LafeLabs/quantumnoisedotorg/geometron/symbolfeed/symbol1696459947.png

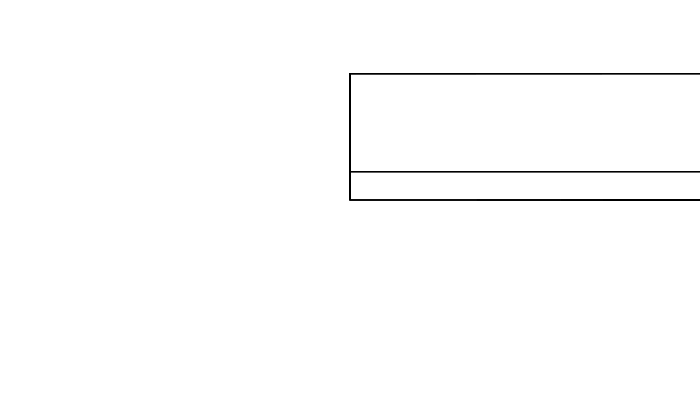
geometron/symbolfeed/symbol1696459947.png
