LafeLabs/quantumnoisedotorg/geometron/symbolfeed/symbol1696465862.png

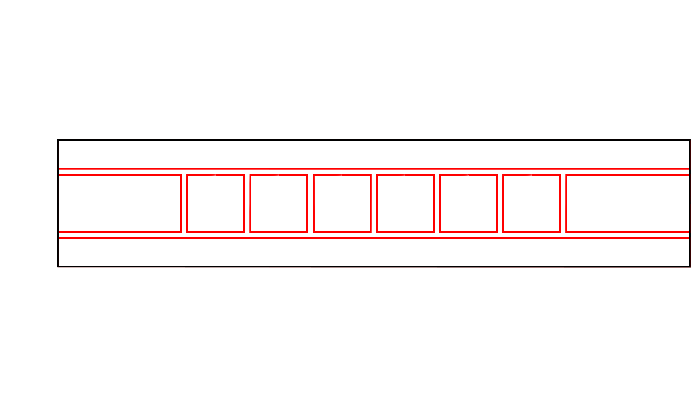
geometron/symbolfeed/symbol1696465862.png
