LafeLabs/quantumnoisedotorg/geometron/symbolfeed/symbol1696466057.png

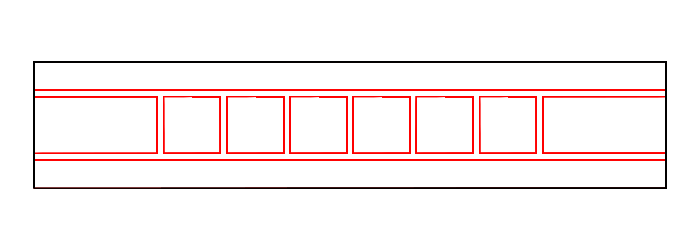
geometron/symbolfeed/symbol1696466057.png
