LafeLabs/quantumnoisedotorg/geometron/symbolfeed/symbol1696466279.png

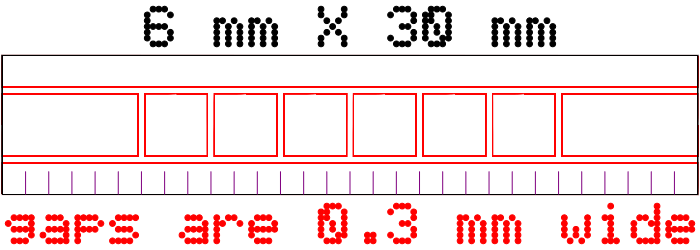
geometron/symbolfeed/symbol1696466279.png
