LafeLabs/quantumnoisedotorg/the-book-of-noise/trashmagic/BOOK-OF-NOISE.png

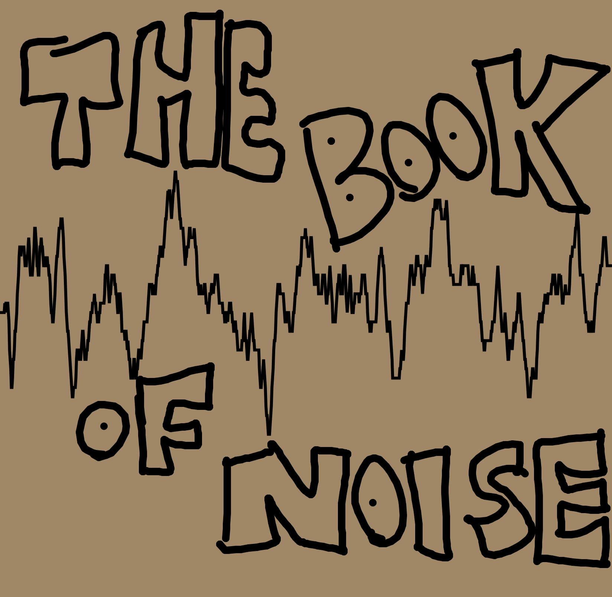
the-book-of-noise/trashmagic/BOOK-OF-NOISE.png
