LafeLabs/quantumnoisedotorg/trashmagic/filter-photo.png

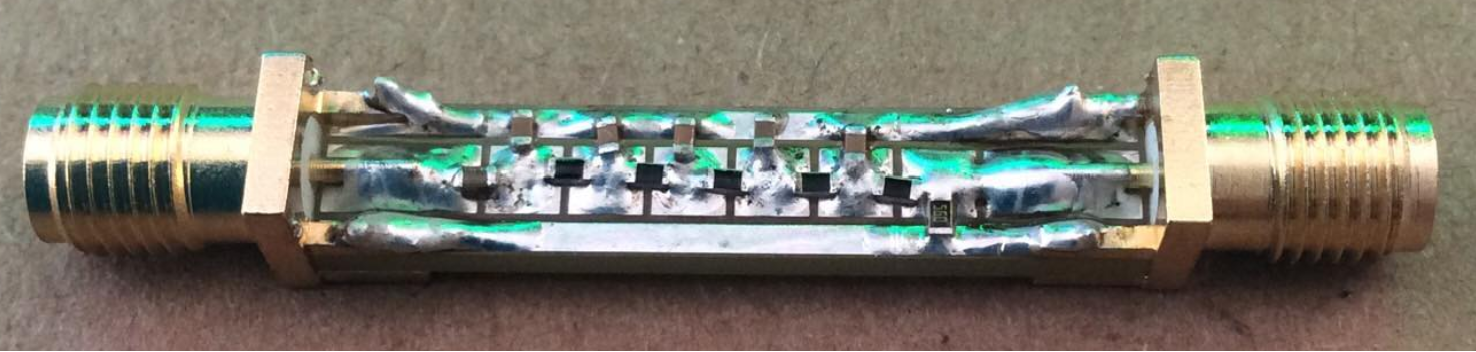
trashmagic/filter-photo.png
