LafeLabs/quantumnoisedotorg/trashmagic/graphene-black-2.png

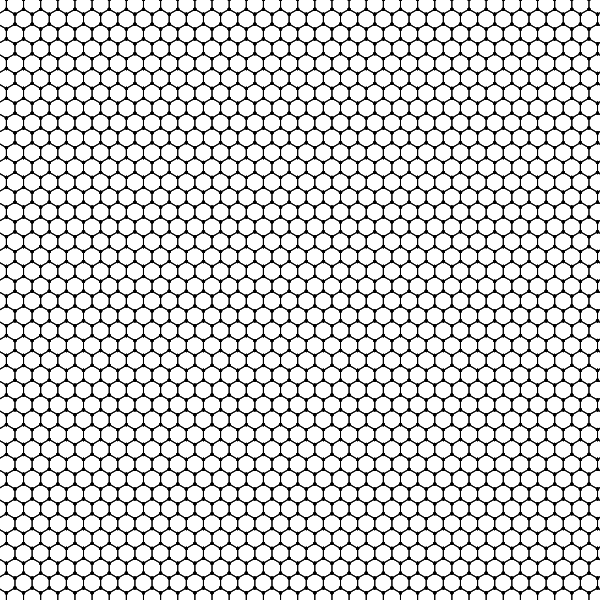
trashmagic/graphene-black-2.png
