LafeLabs/quantumnoisedotorg/trashmagic/graphene-black-3.png

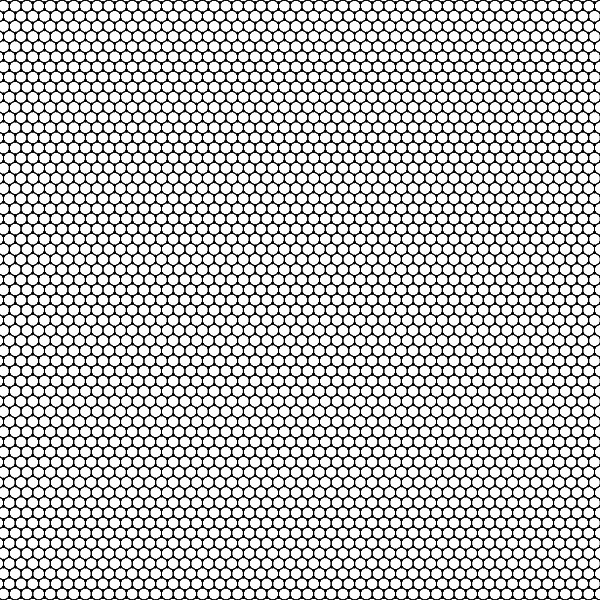
trashmagic/graphene-black-3.png
