LafeLabs/quantumnoisedotorg/trashmagic/graphene-black-4.png

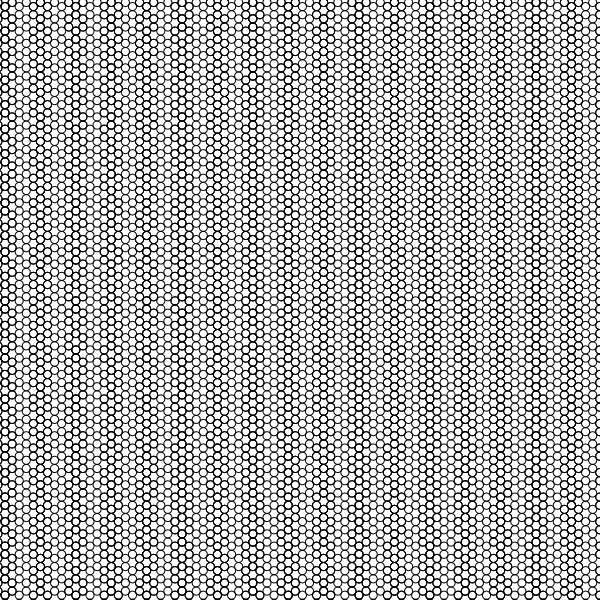
trashmagic/graphene-black-4.png
