LafeLabs/quantumnoisedotorg/trashmagic/graphene-rainbow-1.png

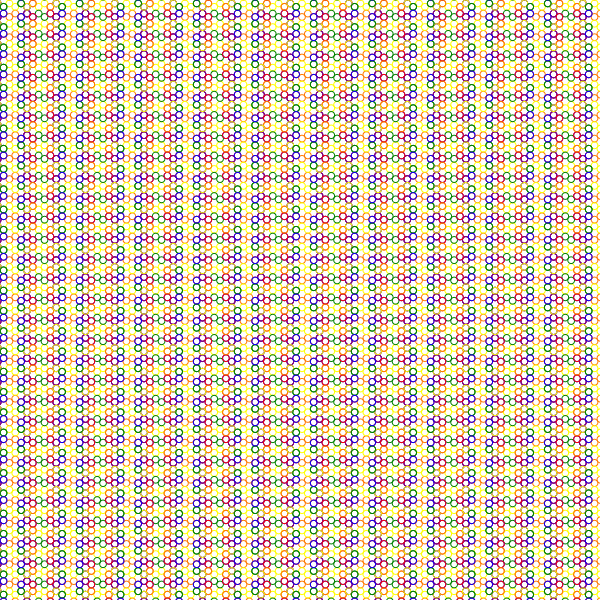
trashmagic/graphene-rainbow-1.png
