LafeLabs/quantumnoisedotorg/trashmagic/merlock/MER_Tarot1.jpg

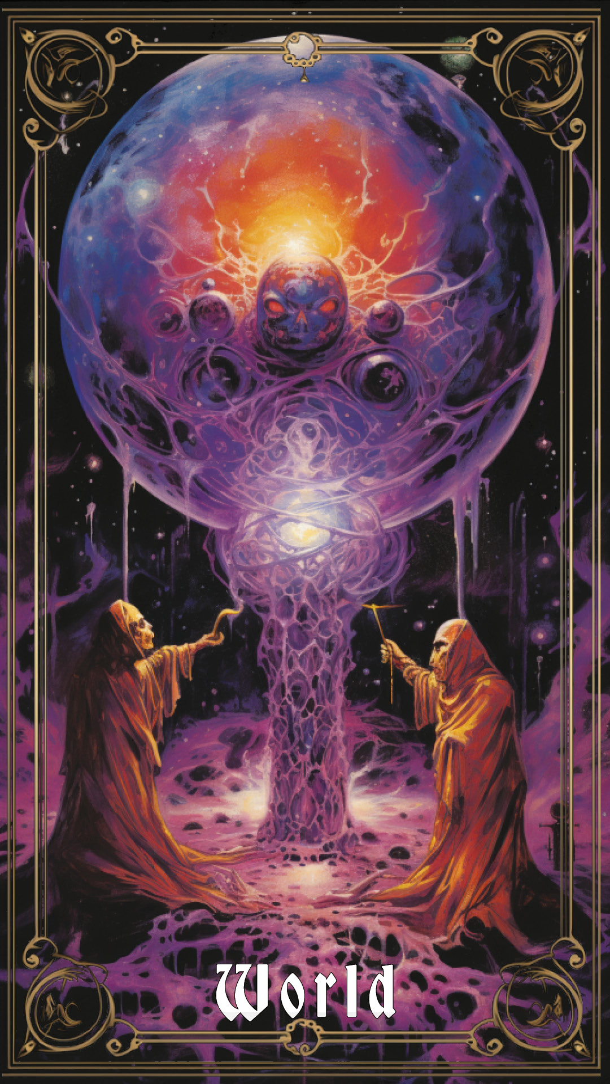
trashmagic/merlock/MER_Tarot1.jpg
