LafeLabs/quantumnoisedotorg/trashmagic/merlock/MER_Tarot3.jpg

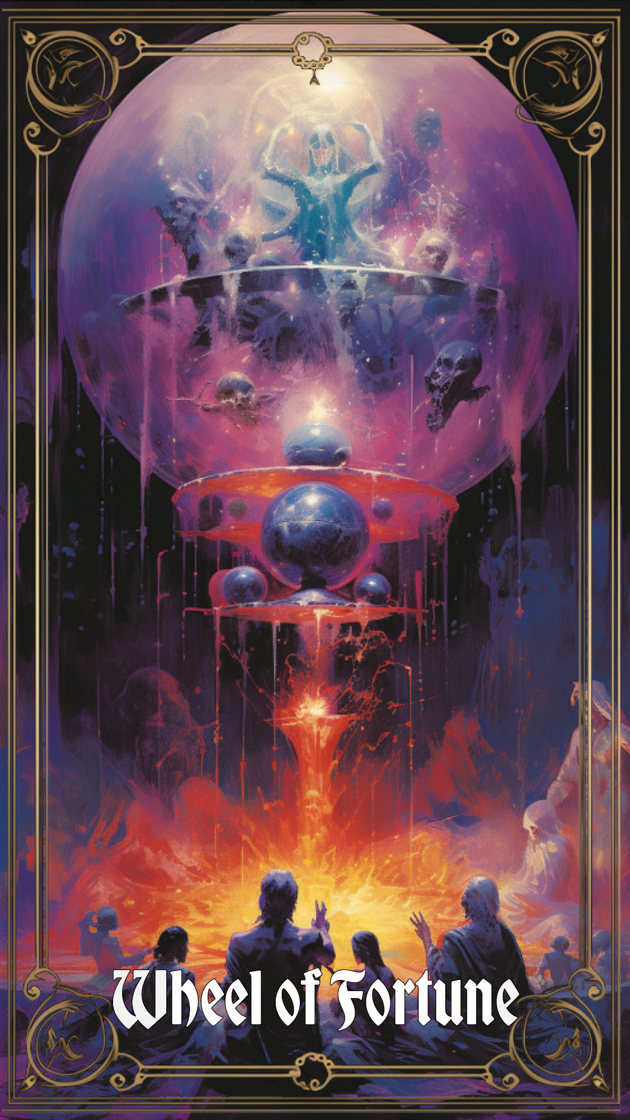
trashmagic/merlock/MER_Tarot3.jpg
