LafeLabs/quantumnoisedotorg/trashmagic/merlock/MER_Tarot4.jpg

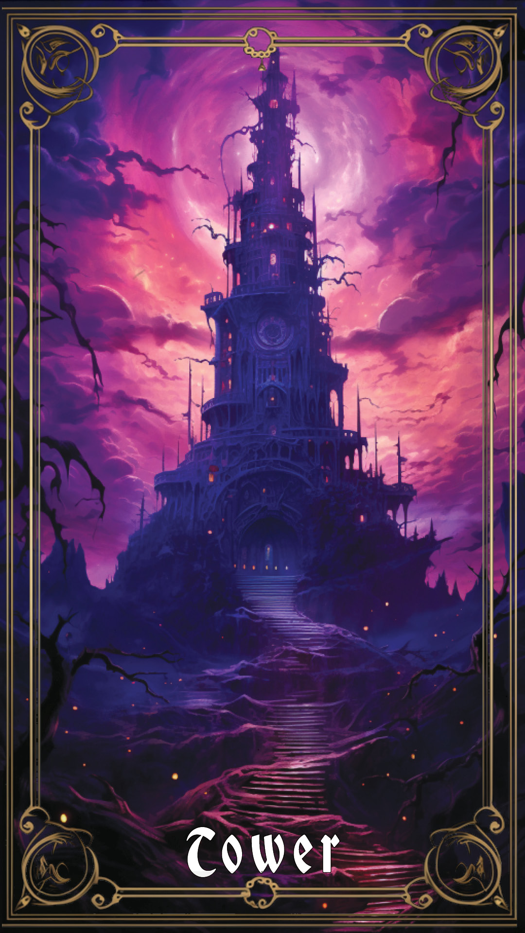
trashmagic/merlock/MER_Tarot4.jpg
