LafeLabs/quantumnoisedotorg/trashmagic/merlock/MER_Tarot5.jpg

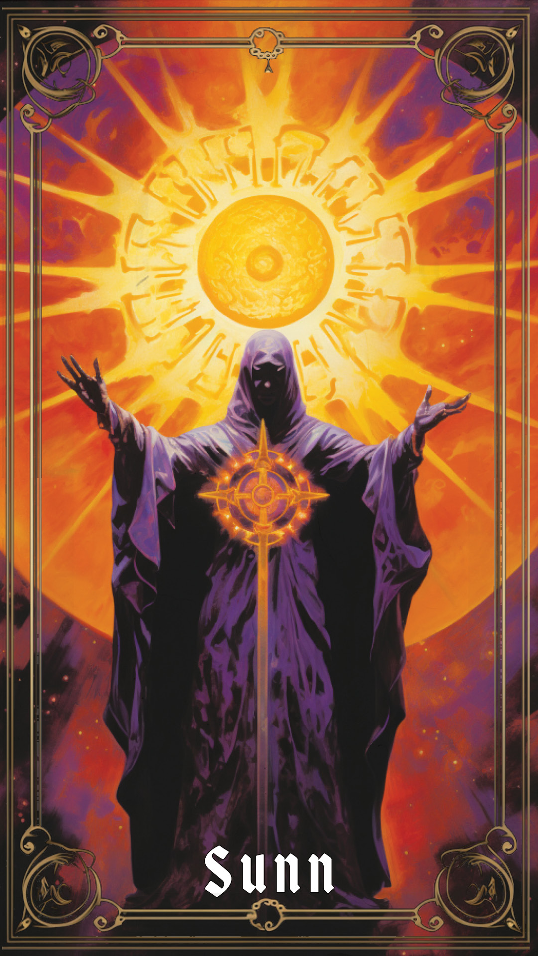
trashmagic/merlock/MER_Tarot5.jpg
