LafeLabs/quantumnoisedotorg/trashmagic/merlock/MER_Tarot6.jpg

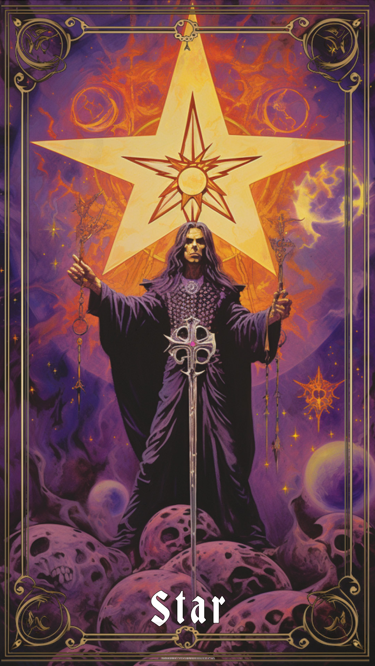
trashmagic/merlock/MER_Tarot6.jpg
