LafeLabs/quantumnoisedotorg/trashmagic/merlock/MER_Tarot7.jpg

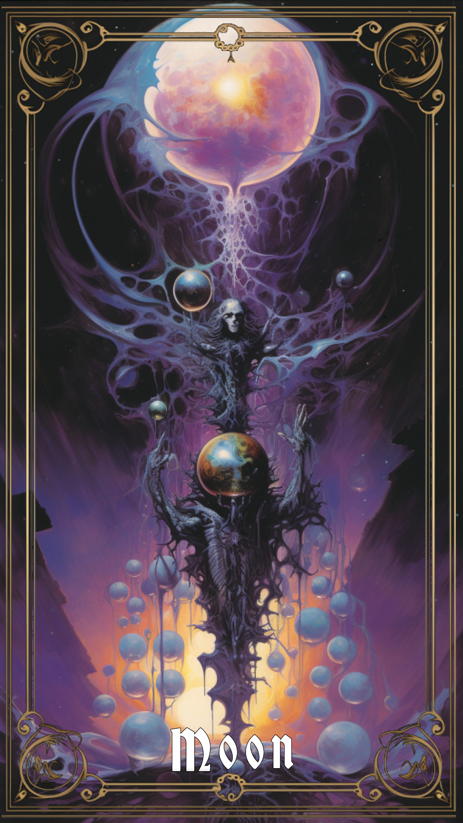
trashmagic/merlock/MER_Tarot7.jpg
