LafeLabs/quantumnoisedotorg/trashmagic/merlock/MER_Tarot8.jpg

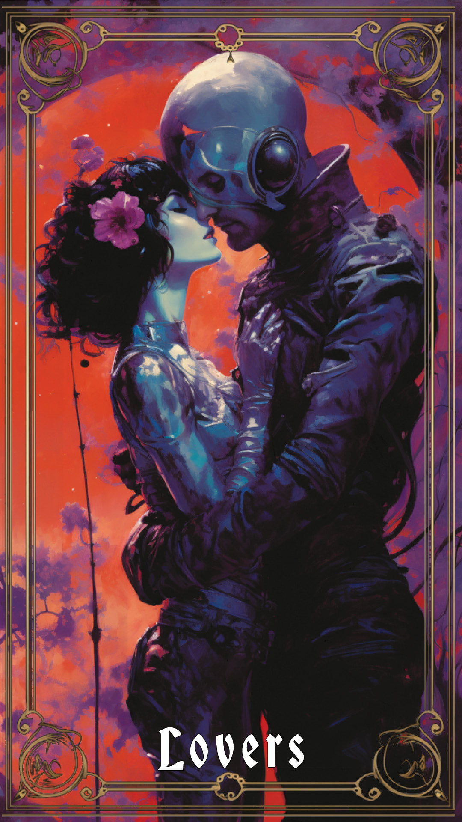
trashmagic/merlock/MER_Tarot8.jpg
