LafeLabs/quantumnoisedotorg/trashmagic/merlock/MER_Tarot9.jpg

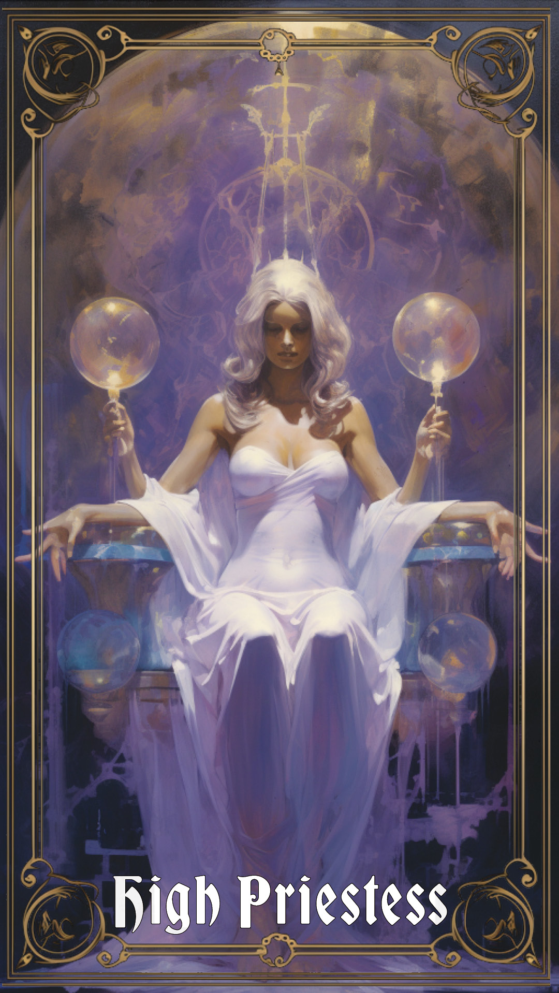
trashmagic/merlock/MER_Tarot9.jpg
