LafeLabs/quantumnoisedotorg/trashmagic/merlock/MER_Tarot10.jpg

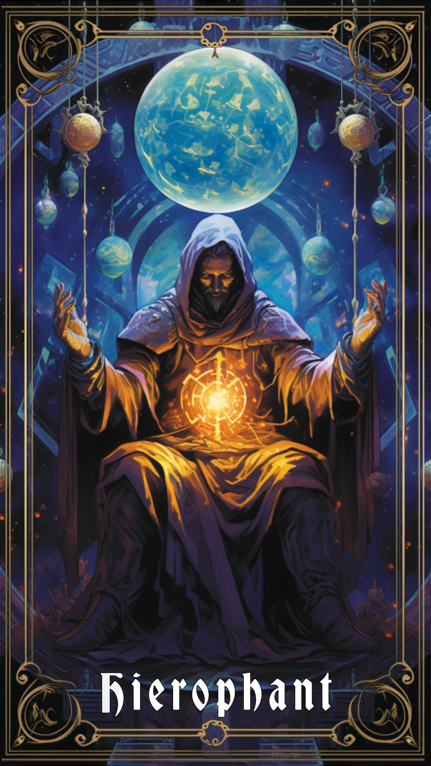
trashmagic/merlock/MER_Tarot10.jpg
