LafeLabs/quantumnoisedotorg/trashmagic/merlock/MER_Tarot11.jpg

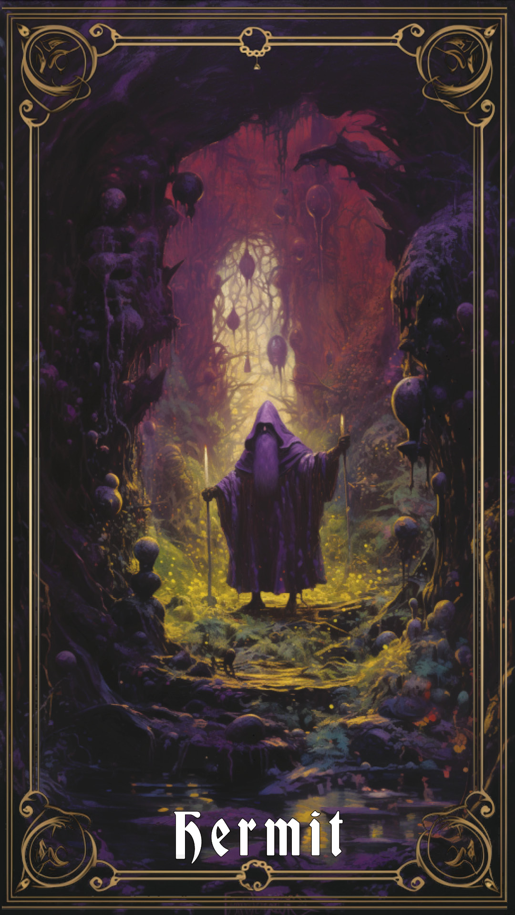
trashmagic/merlock/MER_Tarot11.jpg
