LafeLabs/quantumnoisedotorg/trashmagic/merlock/MER_Tarot12.jpg

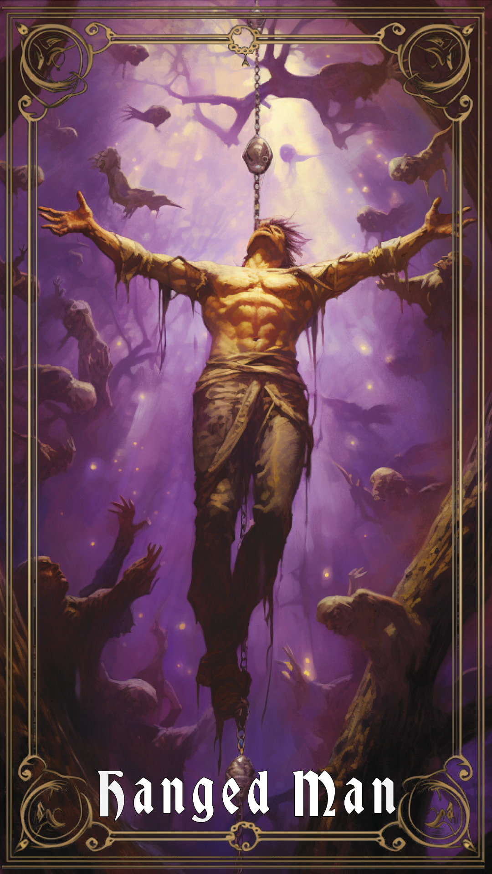
trashmagic/merlock/MER_Tarot12.jpg
