LafeLabs/quantumnoisedotorg/trashmagic/merlock/MER_Tarot14.jpg

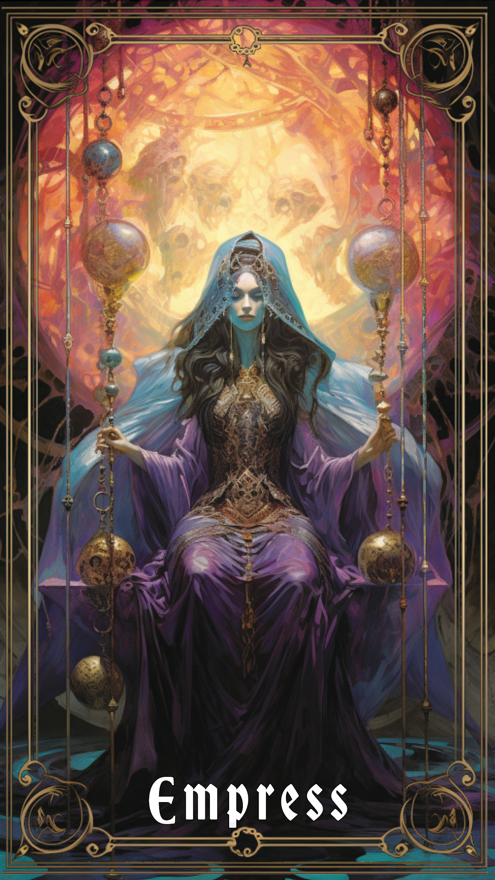
trashmagic/merlock/MER_Tarot14.jpg
