LafeLabs/quantumnoisedotorg/trashmagic/merlock/MER_Tarot15.jpg

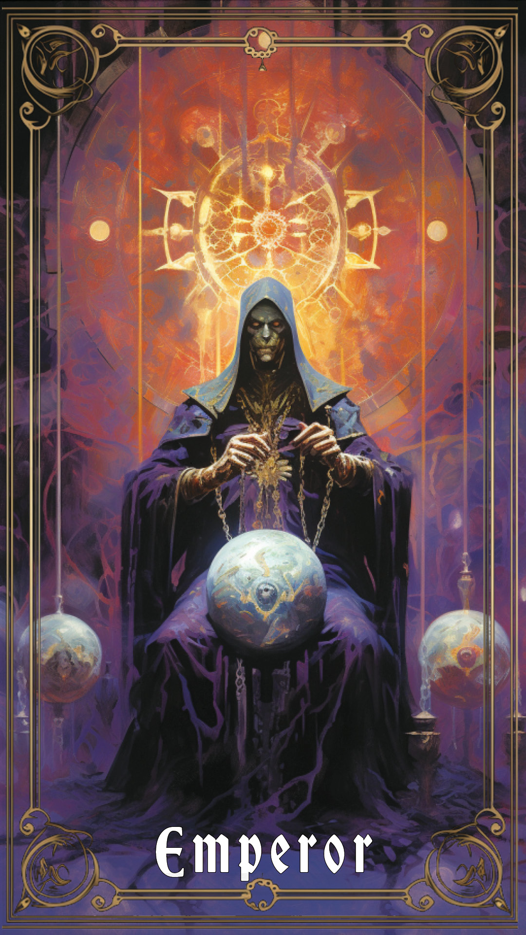
trashmagic/merlock/MER_Tarot15.jpg
