LafeLabs/quantumnoisedotorg/trashmagic/merlock/MER_Tarot16.jpg

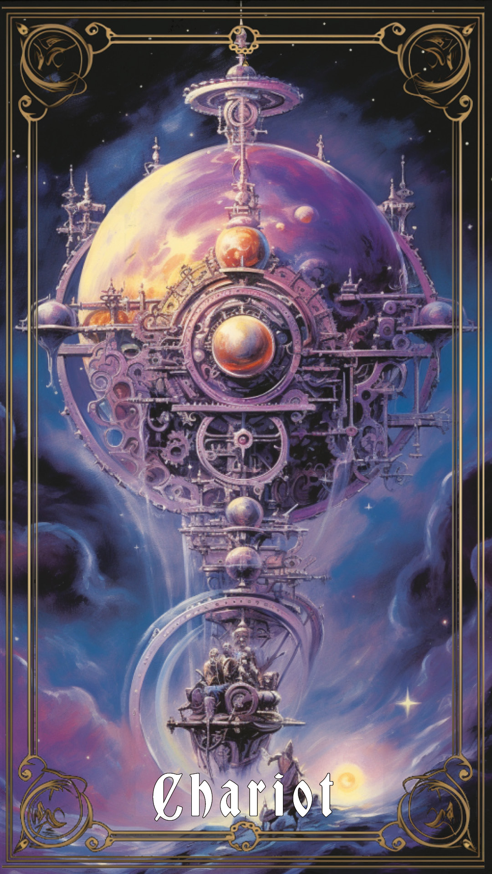
trashmagic/merlock/MER_Tarot16.jpg
