LafeLabs/quantumnoisedotorg/trashmagic/merlock/MER_Tarot17.jpg

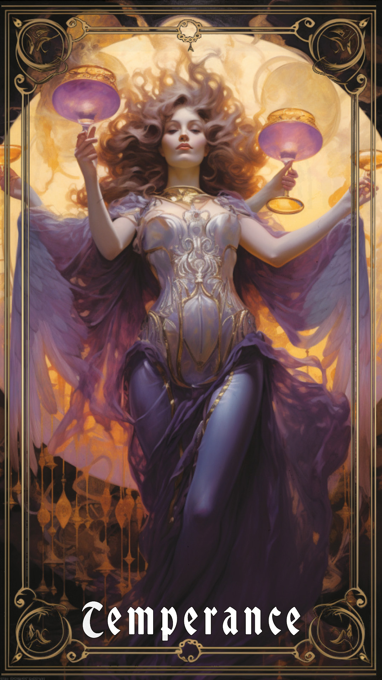
trashmagic/merlock/MER_Tarot17.jpg
