LafeLabs/quantumnoisedotorg/trashmagic/merlock/MER_Tarot18.jpg

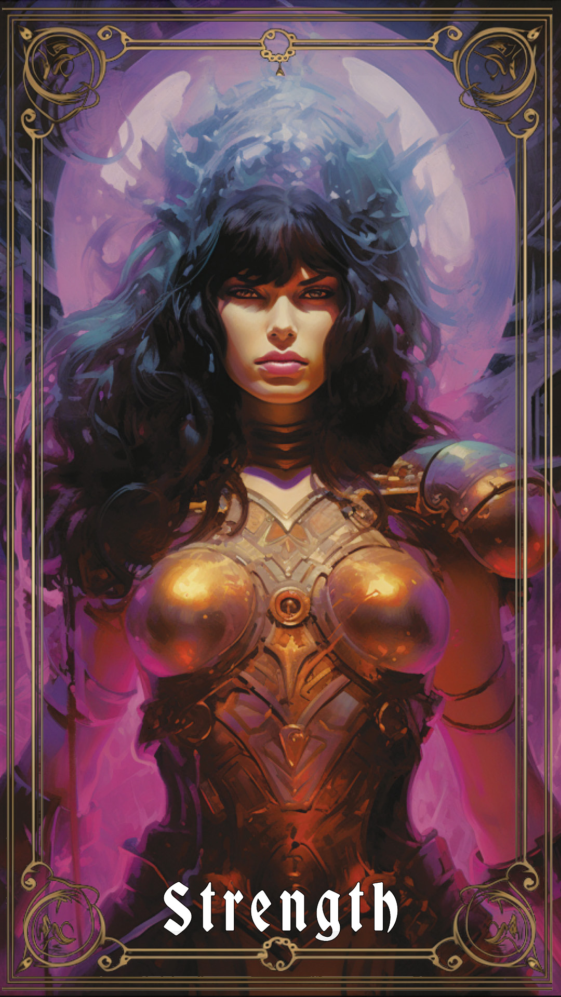
trashmagic/merlock/MER_Tarot18.jpg
