LafeLabs/quantumnoisedotorg/trashmagic/merlock/MER_Tarot19.jpg

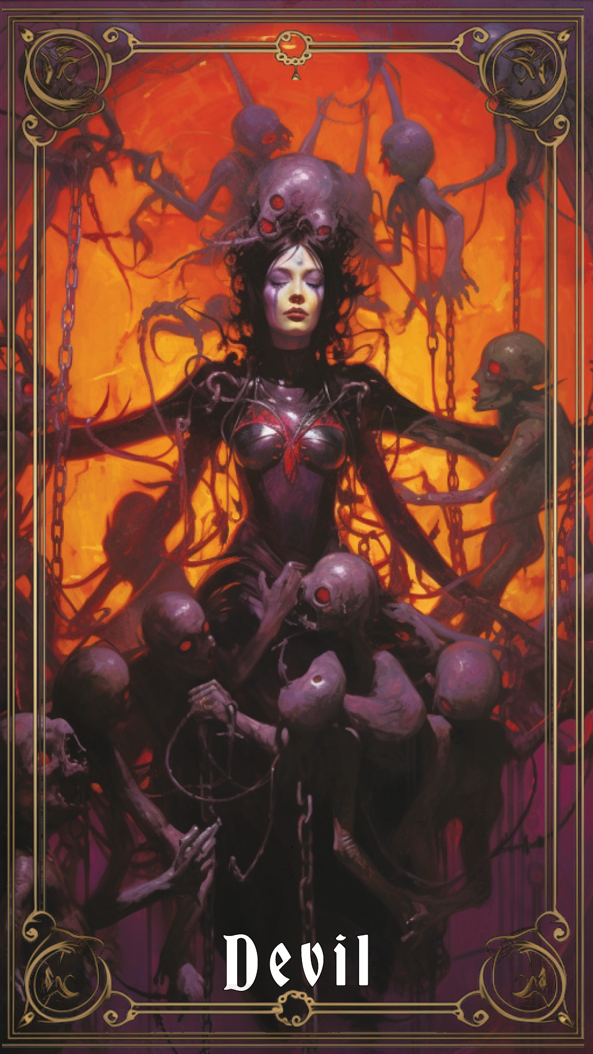
trashmagic/merlock/MER_Tarot19.jpg
