LafeLabs/quantumnoisedotorg/trashmagic/merlock/MER_Tarot20.jpg

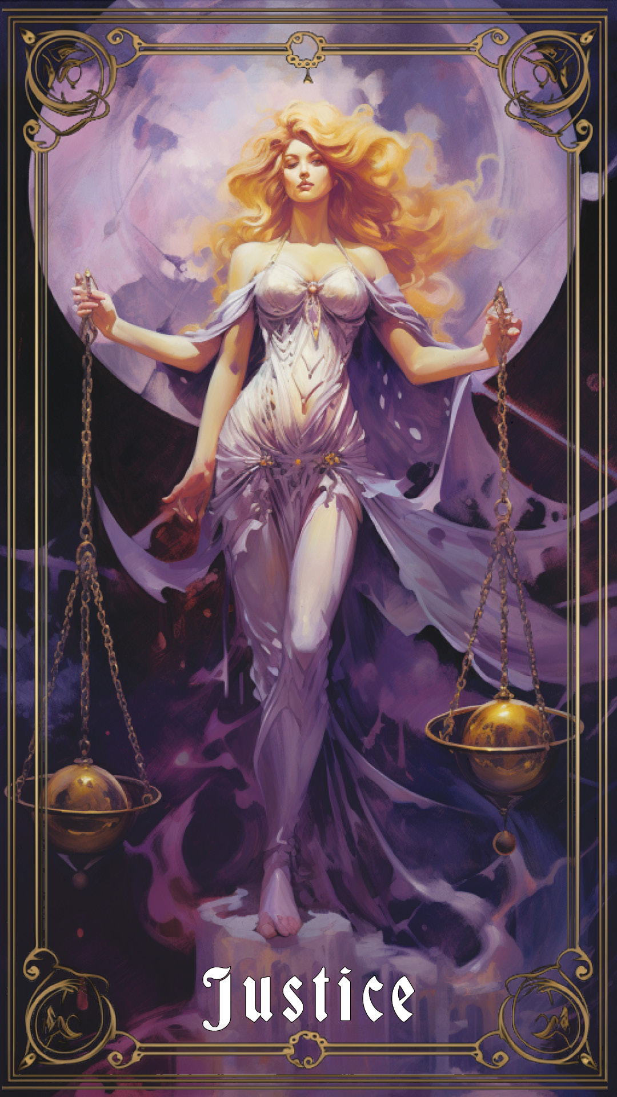
trashmagic/merlock/MER_Tarot20.jpg
