LafeLabs/quantumnoisedotorg/trashmagic/merlock/MER_Tarot22.jpg

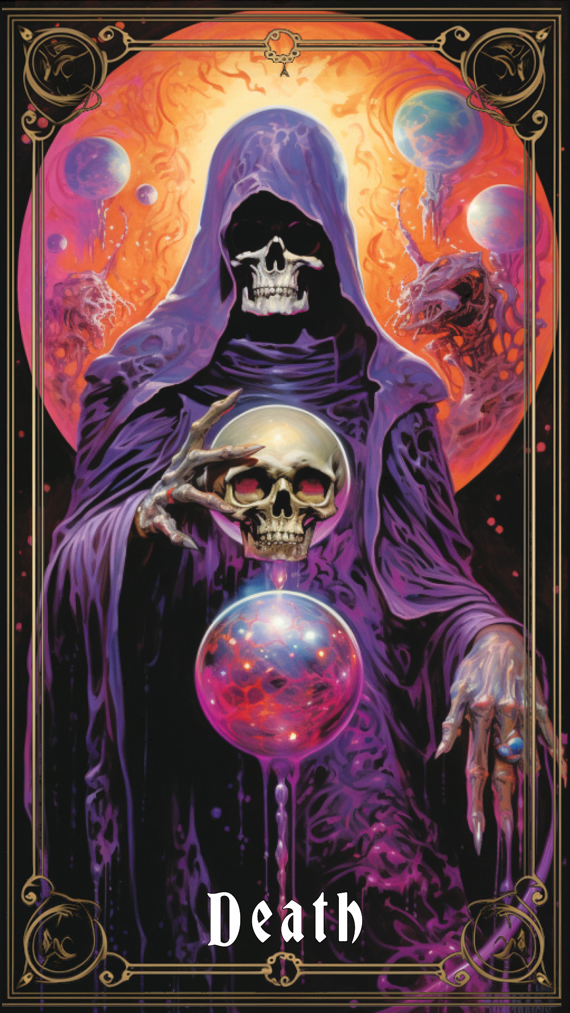
trashmagic/merlock/MER_Tarot22.jpg
