LafeLabs/quantumnoisedotorg/trashmagic/pcb-launch-photo2.png

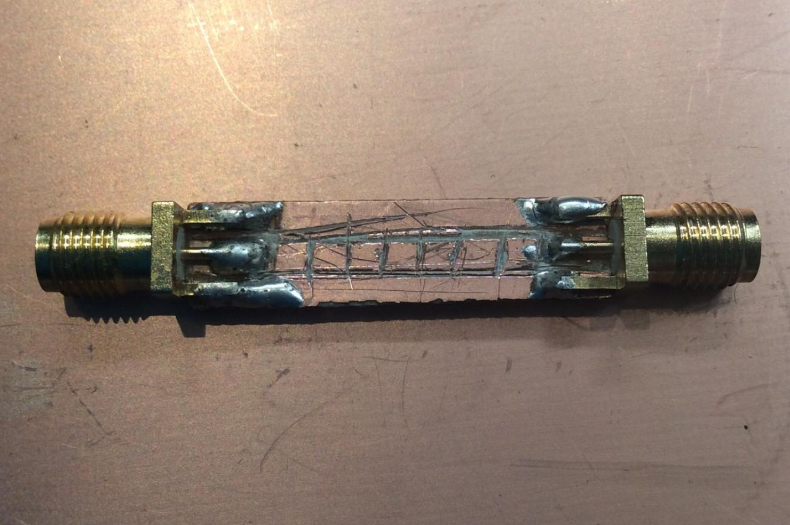
trashmagic/pcb-launch-photo2.png
