LafeLabs/quantumnoisedotorg/trashmagic/pcb-layout-screenshot.png

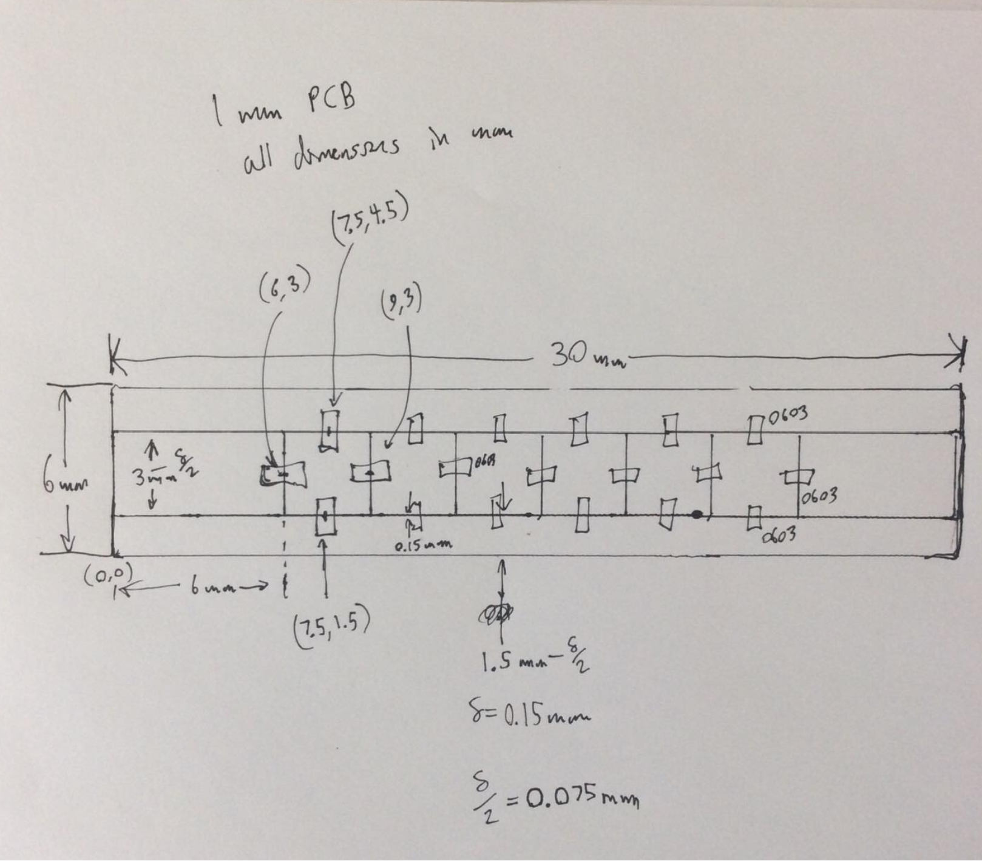
trashmagic/pcb-layout-screenshot.png
