LafeLabs/quantumnoisedotorg/trashmagic/QCHAIN1.png

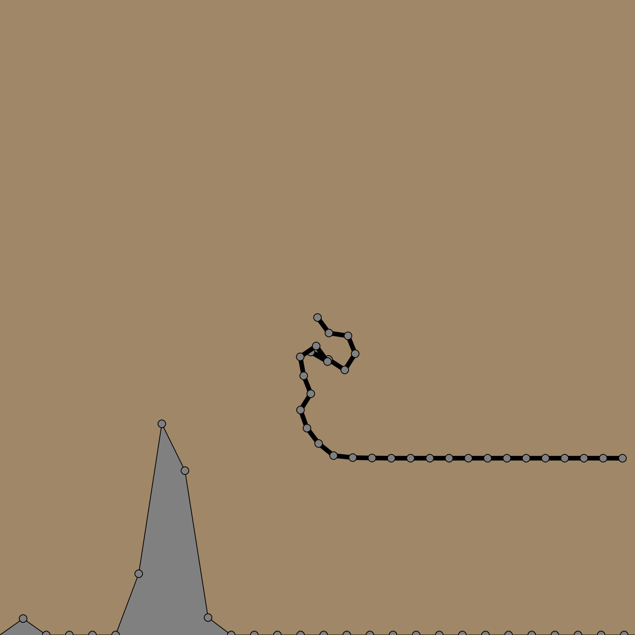
trashmagic/QCHAIN1.png
