LafeLabs/quantumnoisedotorg/trashmagic/QCHAIN2.png

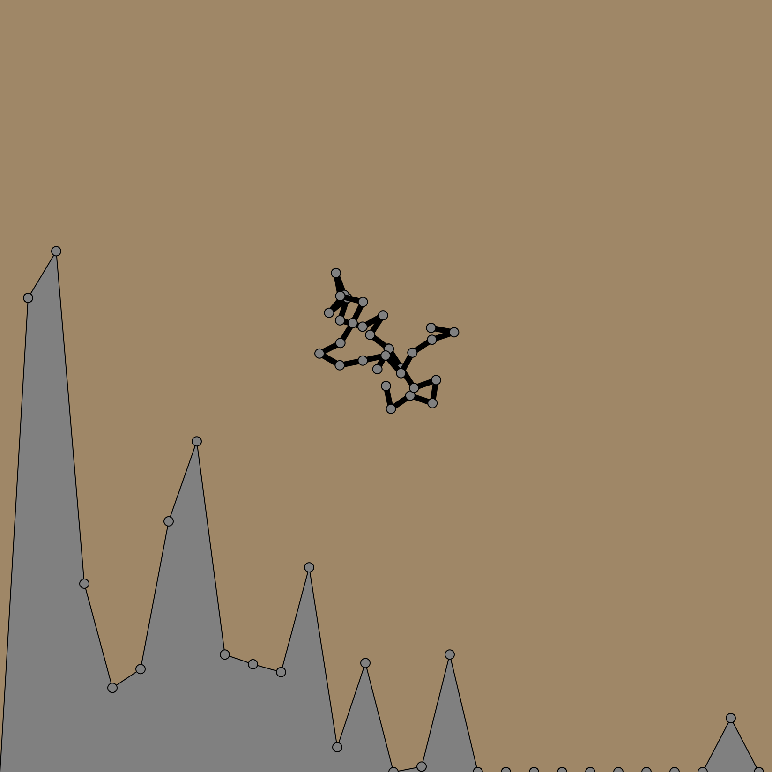
trashmagic/QCHAIN2.png
