LafeLabs/quantumnoisedotorg/trashmagic/QCHAIN3.png

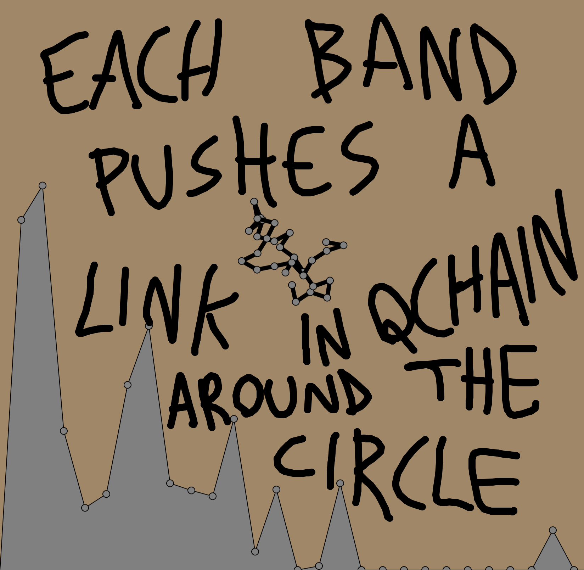
trashmagic/QCHAIN3.png
