LafeLabs/quantumnoisedotorg/trashmagic/rampsquare1.png

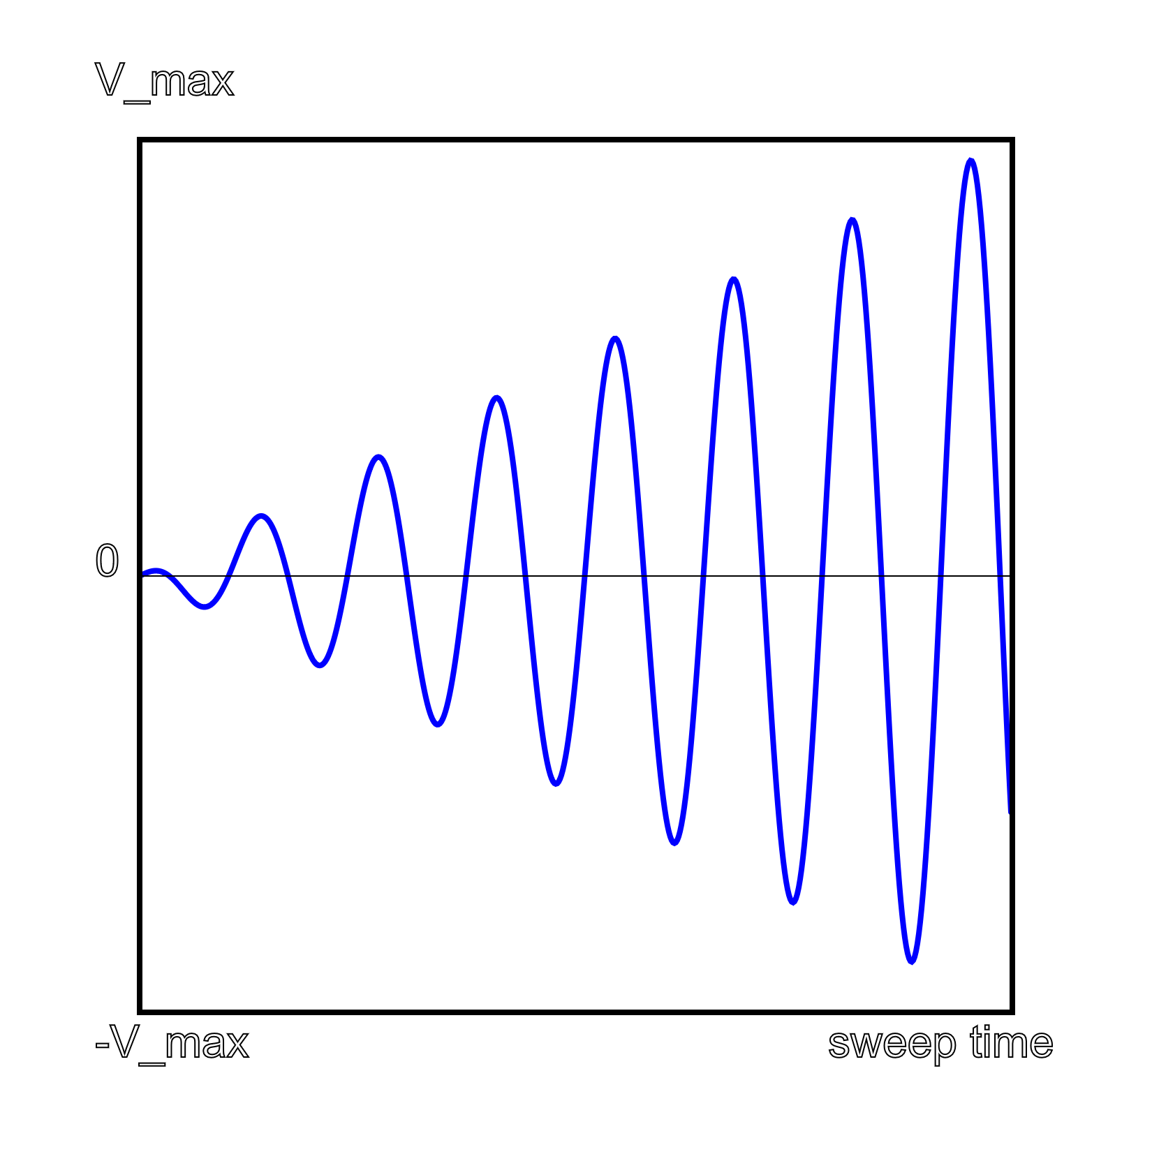
trashmagic/rampsquare1.png
