LafeLabs/quantumnoisedotorg/trashmagic/rampsquare2.png

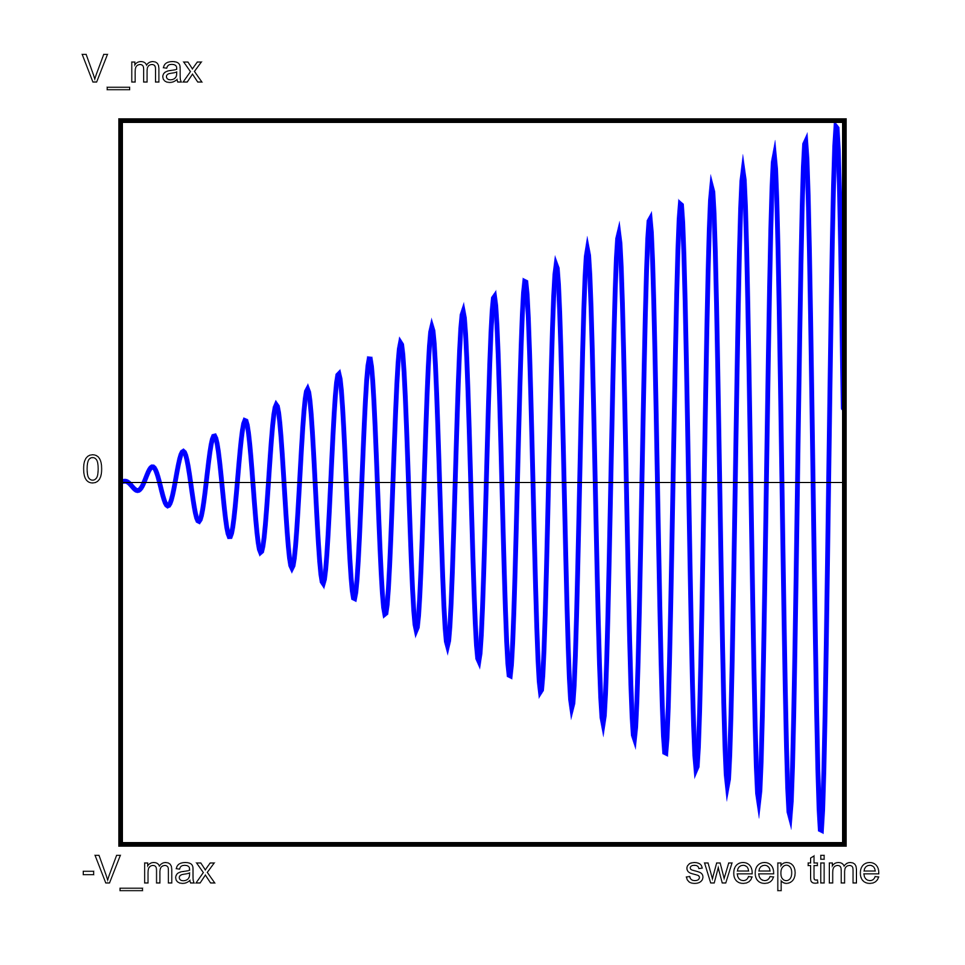
trashmagic/rampsquare2.png
