LafeLabs/quantumnoisedotorg/trashmagic/rock-n-roll-plots2.png

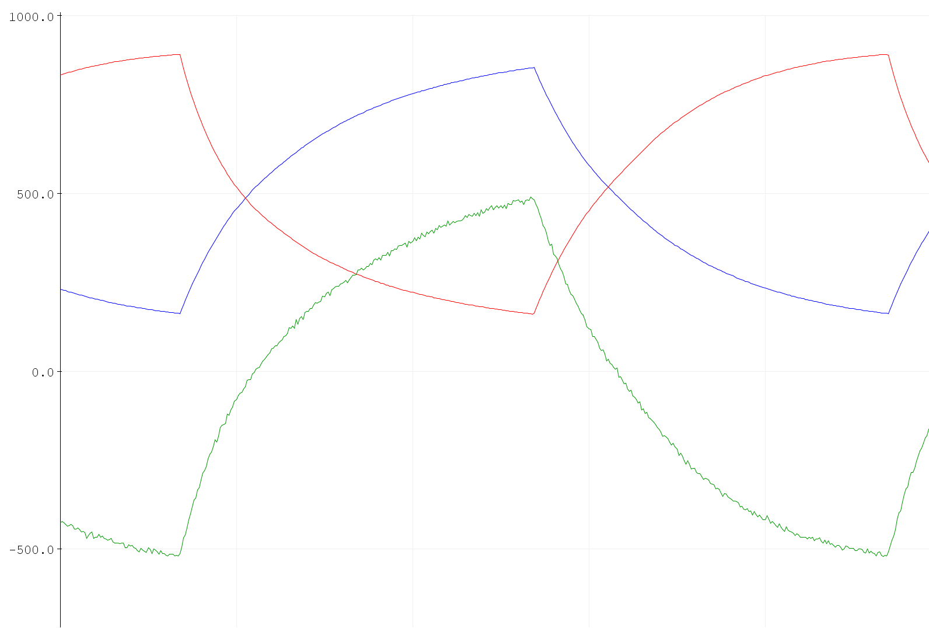
trashmagic/rock-n-roll-plots2.png
