LafeLabs/quantumnoisedotorg/trashmagic/rock-n-roll-plots.png

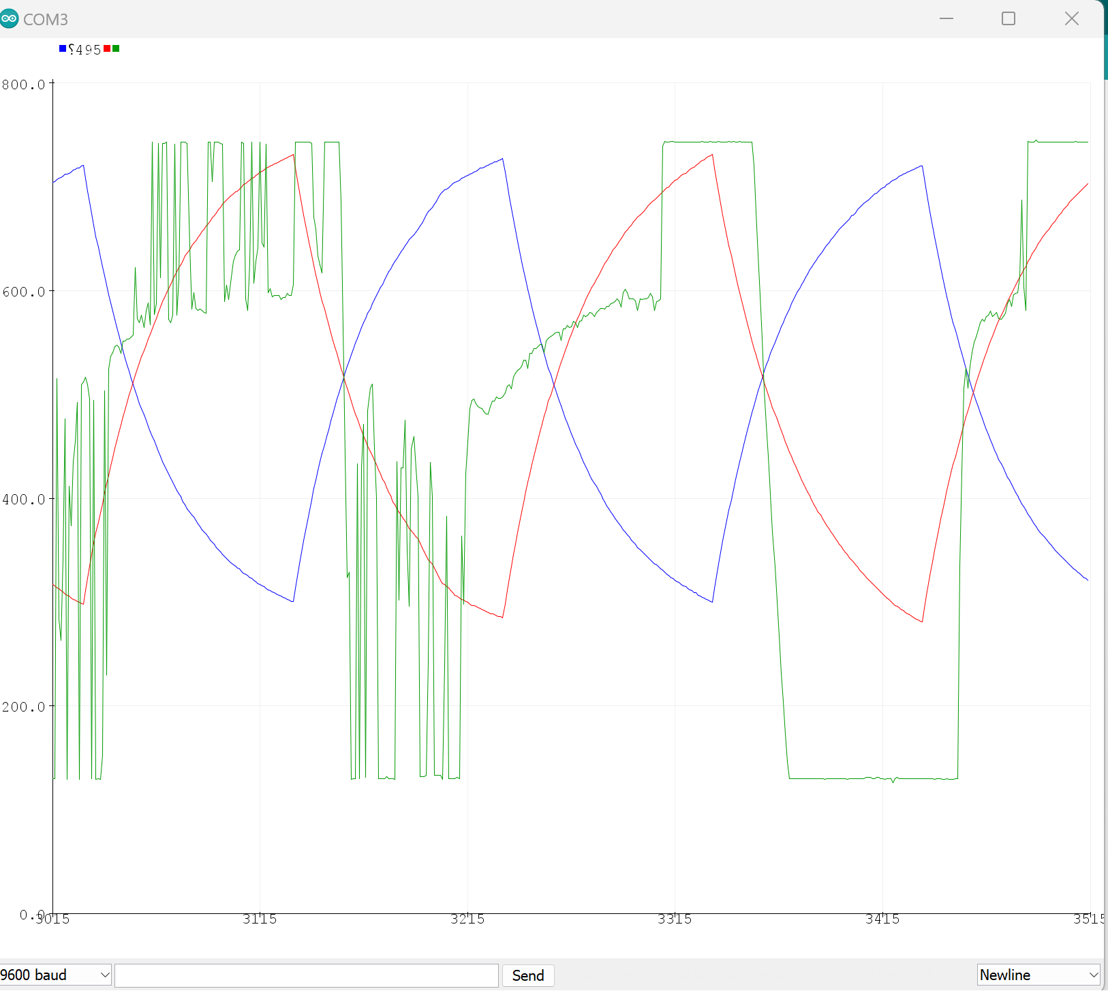
trashmagic/rock-n-roll-plots.png
