LafeLabs/quantumnoisedotorg/trashmagic/rock-n-roll-square-mud.png

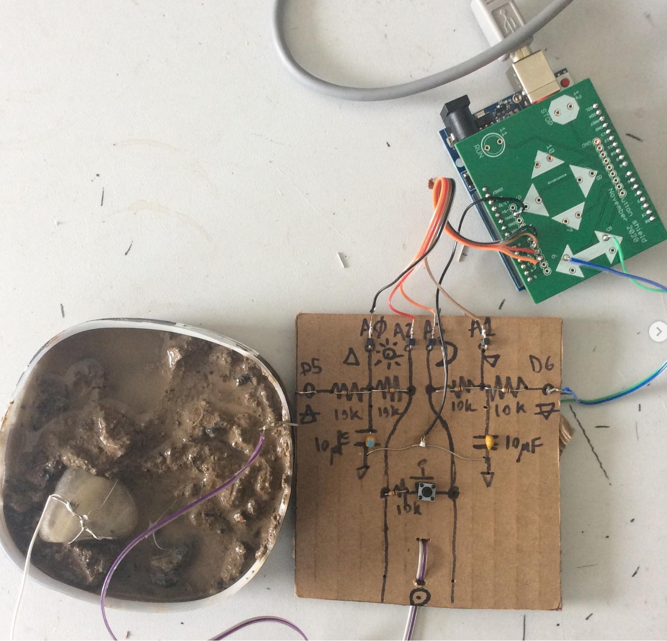
trashmagic/rock-n-roll-square-mud.png
