LafeLabs/quantumnoisedotorg/trashmagic/square1695745236-fuzz.png

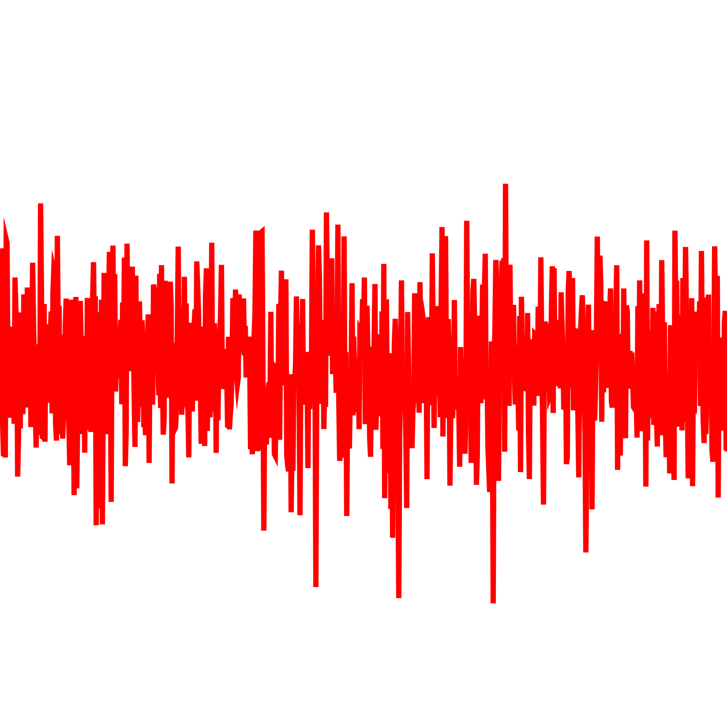
trashmagic/square1695745236-fuzz.png
