LafeLabs/quantumnoisedotorg/trashmagic/sweepcurves1.png

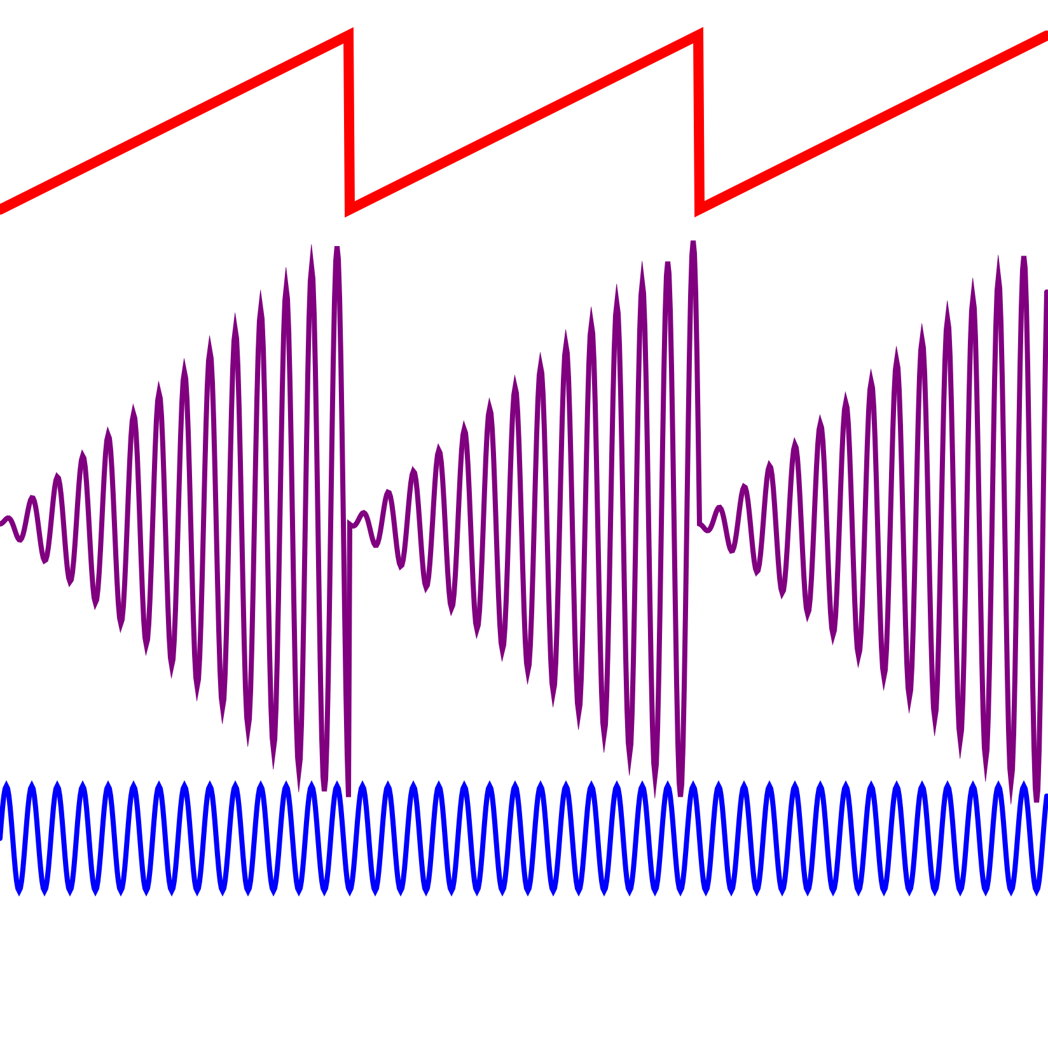
trashmagic/sweepcurves1.png
