LafeLabs/quantumnoisedotorg/trashmagic/capsule-assembly.png

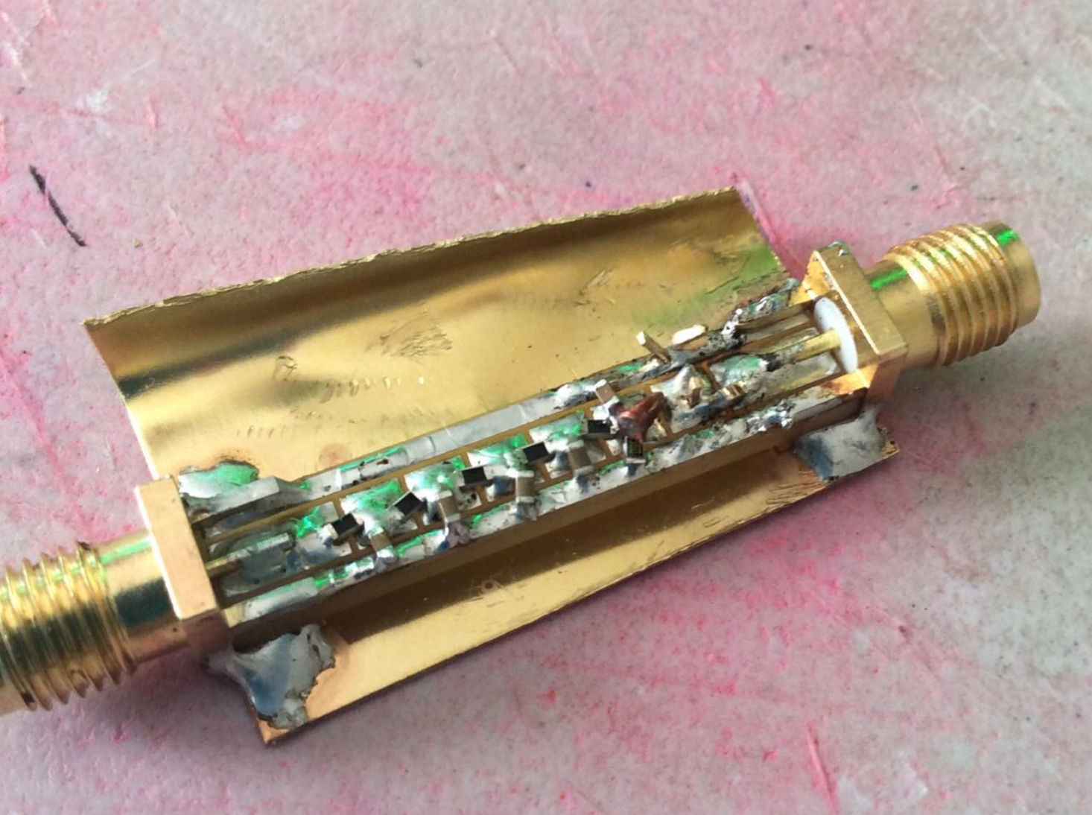
trashmagic/capsule-assembly.png
